attexx/teseo_liv3f_breakout_board/KiCAD/rev. 2/images/01.png

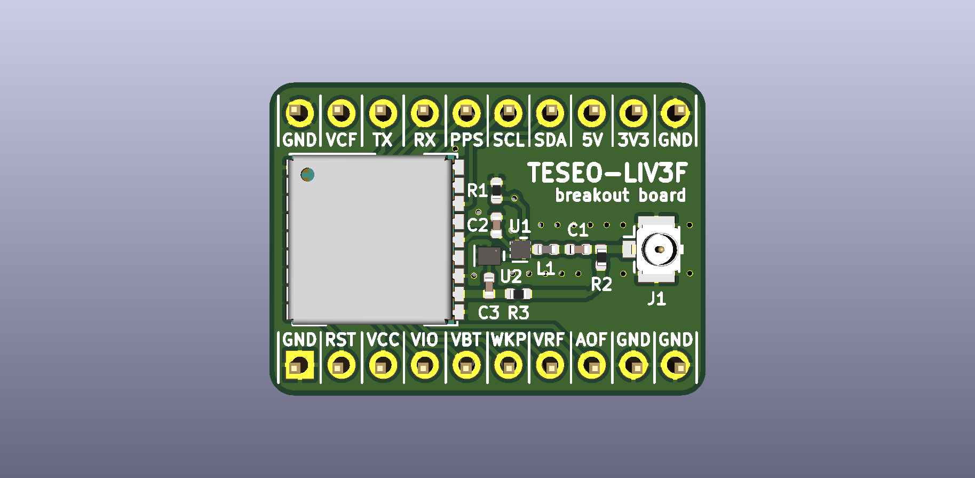
KiCAD/rev. 2/images/01.png
