attexx/teseo_liv3f_breakout_board/KiCAD/rev. 2/images/3x4/01.PNG

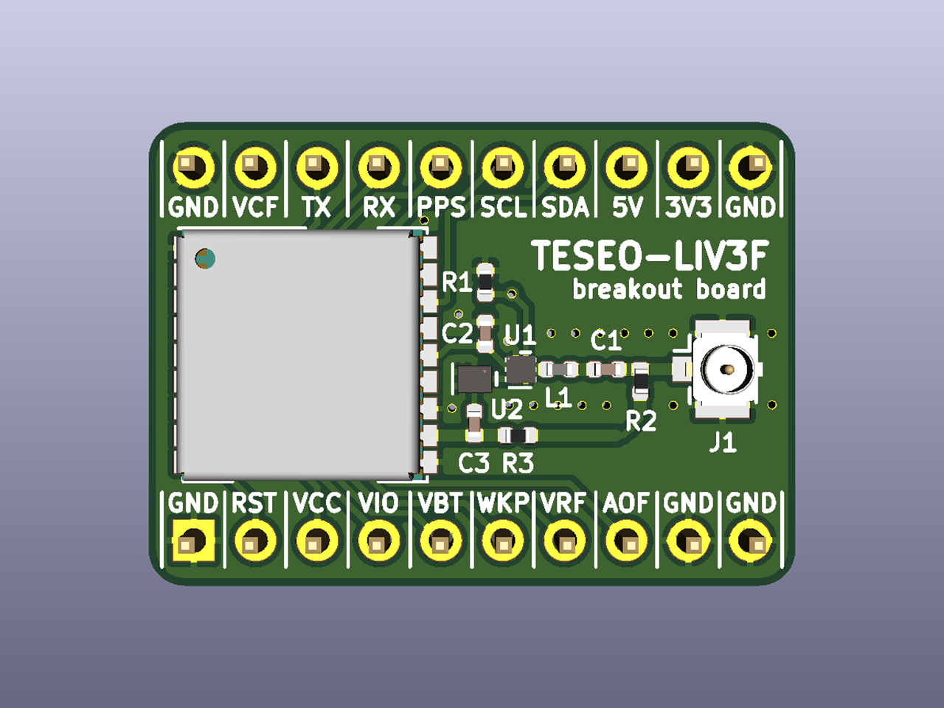
KiCAD/rev. 2/images/3x4/01.PNG
