attexx/teseo_liv3f_breakout_board/KiCAD/rev. 2/images/04.png

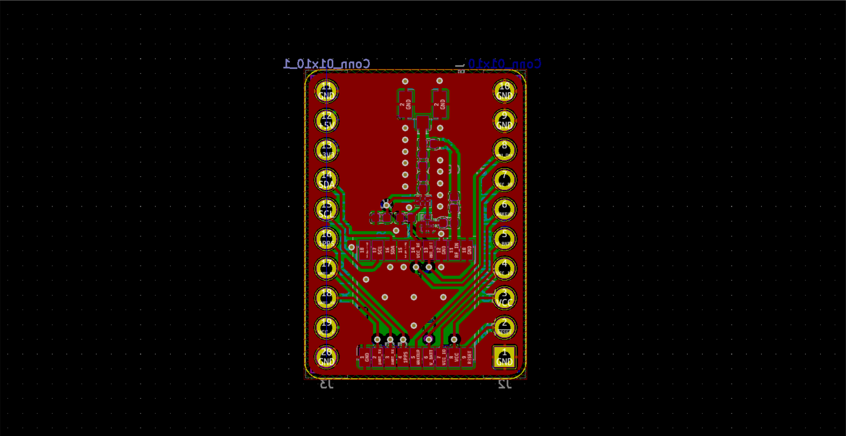
KiCAD/rev. 2/images/04.png
